IuliaGIE/Proiect_TSC/Images/1.png

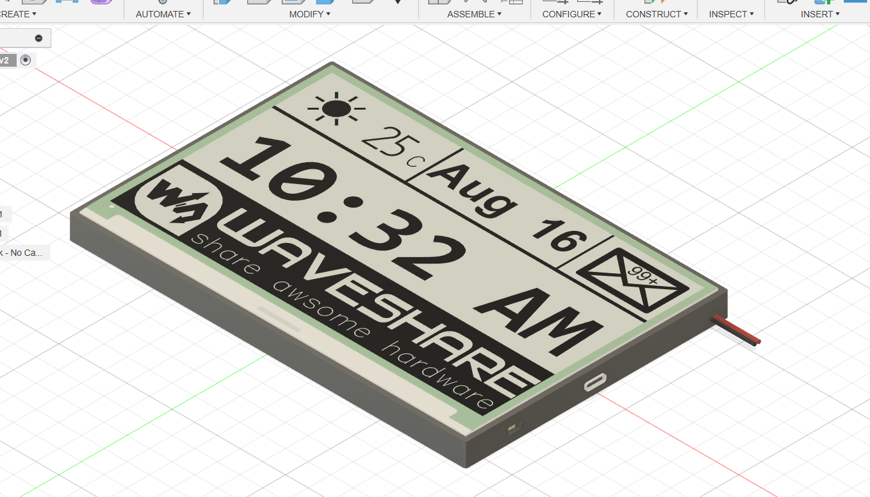
Images/1.png
